gnawali/purple/docs/assignment/images/Capture01.PNG

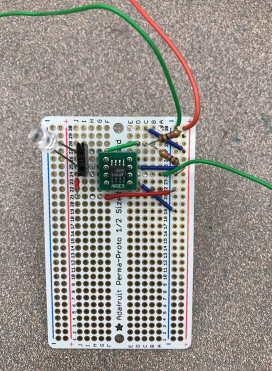
docs/assignment/images/Capture01.PNG
