gnawali/purple/docs/assignment/images/Capture03.PNG

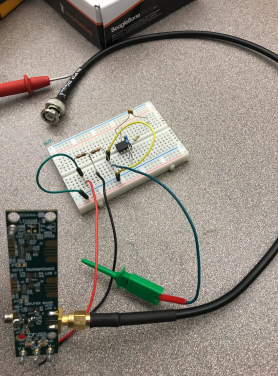
docs/assignment/images/Capture03.PNG
