gnawali/purple/docs/assignment/images/dpkgreconfigure.png

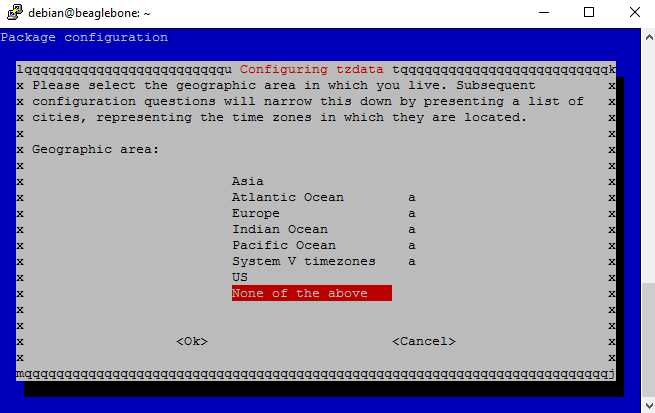
docs/assignment/images/dpkgreconfigure.png
