gnawali/purple/docs/assignment/images/ifconfig.png

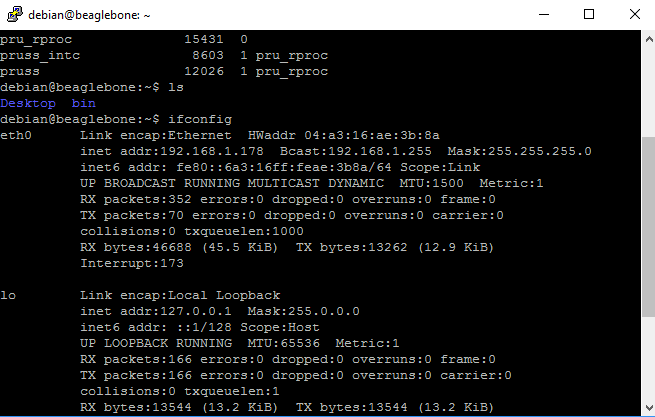
docs/assignment/images/ifconfig.png
