gnawali/purple/pcb/eagle/purple-v2_0-bot.png

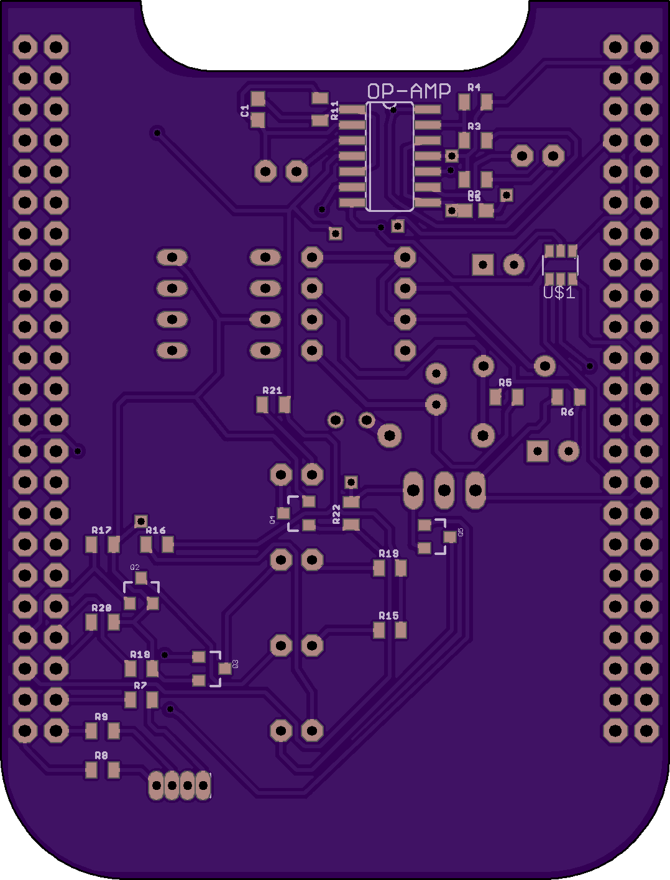
pcb/eagle/purple-v2_0-bot.png
