gnawali/purple/pcb/eagle/purple-v2_0-top.png

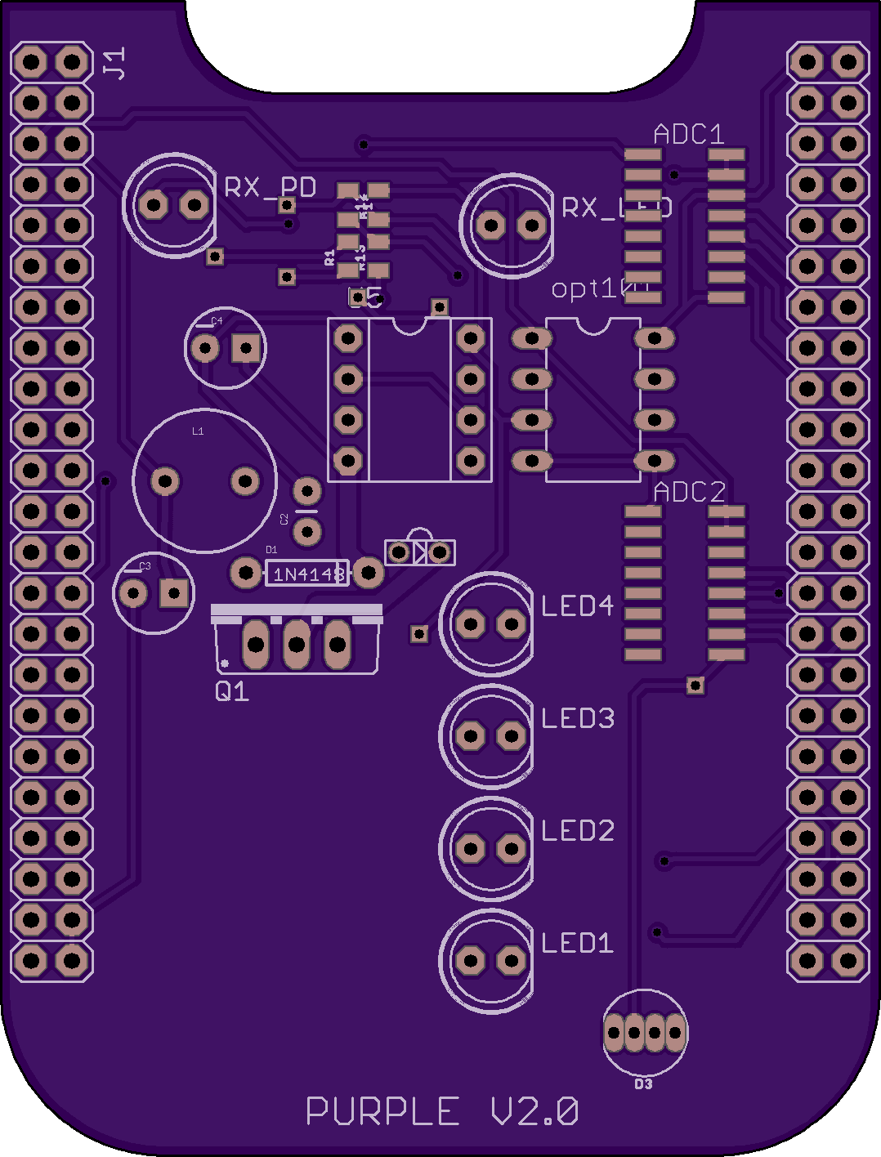
pcb/eagle/purple-v2_0-top.png
